josko7452/qwave-project/software/QWave/Device/DummyDevice.h

//
//   DummyDevice.h
//   QWave
//   Copyright (c) 2012-2013, Bruno Kremel
//   All rights reserved.
//
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
//    THIS SOFTWARE IS PROVIDED BY Bruno Kremel ''AS IS'' AND ANY
//    EXPRESS OR IMPLIED WARRANTIES, INCLUDING, BUT NOT LIMITED TO, THE IMPLIED
//    WARRANTIES OF MERCHANTABILITY AND FITNESS FOR A PARTICULAR PURPOSE ARE
//    DISCLAIMED. IN NO EVENT SHALL Bruno Kremel BE LIABLE FOR ANY
//    DIRECT, INDIRECT, INCIDENTAL, SPECIAL, EXEMPLARY, OR CONSEQUENTIAL DAMAGES
//    (INCLUDING, BUT NOT LIMITED TO, PROCUREMENT OF SUBSTITUTE GOODS OR SERVICES;
//    LOSS OF USE, DATA, OR PROFITS; OR BUSINESS INTERRUPTION) HOWEVER CAUSED AND
//    ON ANY THEORY OF LIABILITY, WHETHER IN CONTRACT, STRICT LIABILITY, OR TORT
//    (INCLUDING NEGLIGENCE OR OTHERWISE) ARISING IN ANY WAY OUT OF THE USE OF THIS
//    SOFTWARE, EVEN IF ADVISED OF THE POSSIBILITY OF SUCH DAMAGE.


#ifndef DUMMYDEVICE_H
#define DUMMYDEVICE_H

#include "AbstractDevice.h"
#include <QSemaphore>

static const int TEST_LENGTH = 10000;

/**
 * @brief The DummyDeviceCapturer class represents capture thread of Dummy Device.
 * This thread is used to asynchronously capture data to leave main event loop time for GUI responses.
 */
class DummyDeviceCapturer : public QObject
{
    Q_OBJECT
    uint8_t currentAdc1data;
    uint8_t currentAdc2data;
    uint8_t currentDigitalData;

    uint8_t* rawAnalogDataAdc1;
    uint8_t* rawAnalogDataAdc2;
    uint16_t* rawDigitalData;
    QSemaphore* dataSemaphore;
    int armedChannels;
    int analogTriggerType1;
    int analogTriggerType2;
    uint8_t analogTriggerValue1;
    uint8_t analogTriggerValue2;
    int digitalTriggerType;
    QVector<uint8_t> digitalTriggerValues;
    QVector<uint8_t> values;
    QVector<uint8_t> top;
    QVector<uint8_t> bottom;
    int attenuator1;
    int attenuator2;
    int channel1co;
    int channel2co;
    int ratioBase;
    int style;
signals:
    void newDataLength(unsigned int dataLengths);
    void end();
public:
    DummyDeviceCapturer(int armedChannels, int analogTriggerType1,  int analogTriggerType2, uint8_t analogTriggerValue1, uint8_t analogTriggerValue2,
                        int digitalTriggerType, QVector<uint8_t> digitalTriggerValues, QVector<uint8_t> top, uint8_t* rawAnalogDataAdc1, uint8_t* rawAnalogDataAdc2,
                        QVector<uint8_t> bottom, int attenuator1, int attenuator2, int channel1co, int channel2co, int ratioBase, int style, uint16_t* rawDigitalData, QSemaphore* dataSemaphore) :
        armedChannels(armedChannels),  analogTriggerType1(analogTriggerType1),  analogTriggerValue1(analogTriggerValue1), analogTriggerValue2(analogTriggerValue2),
        digitalTriggerType(digitalTriggerType), digitalTriggerValues(digitalTriggerValues), top(top), bottom(bottom), dataSemaphore(dataSemaphore),
        attenuator1(attenuator1), attenuator2(attenuator2), channel1co(channel1co), channel2co(channel2co), ratioBase(ratioBase), style(style),
        rawAnalogDataAdc1(rawAnalogDataAdc1),
        rawAnalogDataAdc2(rawAnalogDataAdc2),
        rawDigitalData(rawDigitalData) {}
public slots:
    void doDummyCapture();
};

static const char * DEVICE_NAME = "DUMMY";

/**
 * @brief The DummyDevice class represents dummy device, which odesnt connect to hardware device,
 *  but generates data programatically instead.
 */
class DummyDevice : public AbstractDevice
{
    Q_OBJECT

    int period;
    uint8_t rawAnalogDataAdc1[TEST_LENGTH];
    uint8_t rawAnalogDataAdc2[TEST_LENGTH];
    uint16_t rawDigitalData[TEST_LENGTH];
    QSemaphore dataSemaphore;
    QVector<uint8_t*> rawDataList;
    unsigned int dataLength;
    int analogTriggerType1;
    int analogTriggerType2;
    uint8_t analogTriggerValue1;
    uint8_t analogTriggerValue2;
    int digitalTriggerType;
    QVector<uint8_t> digitalTriggerValues;
    QVector<uint8_t> topVref;
    QVector<uint8_t> botVref;
    int attenuator1;
    int attenuator2;
    int channel1co;
    int channel2co;
    int ratioBase;
    int style;
    uint8_t logicSupply;
public:
    DummyDevice(int period = 20, bool simulateFtdiError = false); //ns
    ~DummyDevice();
    int getCapability() { return TWO_ANALOG_ONE_DIGITAL; }
    QVector<uint8_t*> getRawDataList();
    unsigned int getRawDataLength();
    QString getName() { return DEVICE_NAME; }
    void lockData();
    void unlockData();
    void setTrigger(int kind, int type, QVector<uint8_t> values, int channel);
    void setOffsetAndGain(QVector<uint8_t> top, QVector<uint8_t> bottom);
    void setAttenuator(int channel, int attenuator);
    void setCoupling(int channel, int coupling);
    void armDevice(int armedChannels, CaptureController* capc);
    void setDecimation(int ratioBase, int style);
    void setLogicSupply(uint8_t value);
    uint8_t getLogicSupply() { return logicSupply; }
    QPair<int, QVector<uint8_t> > getTrigger(int kind, int channel);
    QPair<QVector<uint8_t>, QVector<uint8_t> > getOffsetAndGain();
    int getAttenuator(int channel);
    int getCoupling(int channel);
    QPair<int, int> getDecimation();
public slots:
    void updateDataLength(unsigned int dataLength);
signals:
    void dataUpdated(); //emited when it is convient to refresh viewport
};

#endif // DUMMYDEVICE_H
